CassioSStella/Robo-Sumo_Eletronica/Exemplo/Sumo_Geral_Modular.kicad_sch

## KiCad design Exemplo/Sumo_Geral_Modular.kicad_sch (2026-05-20)

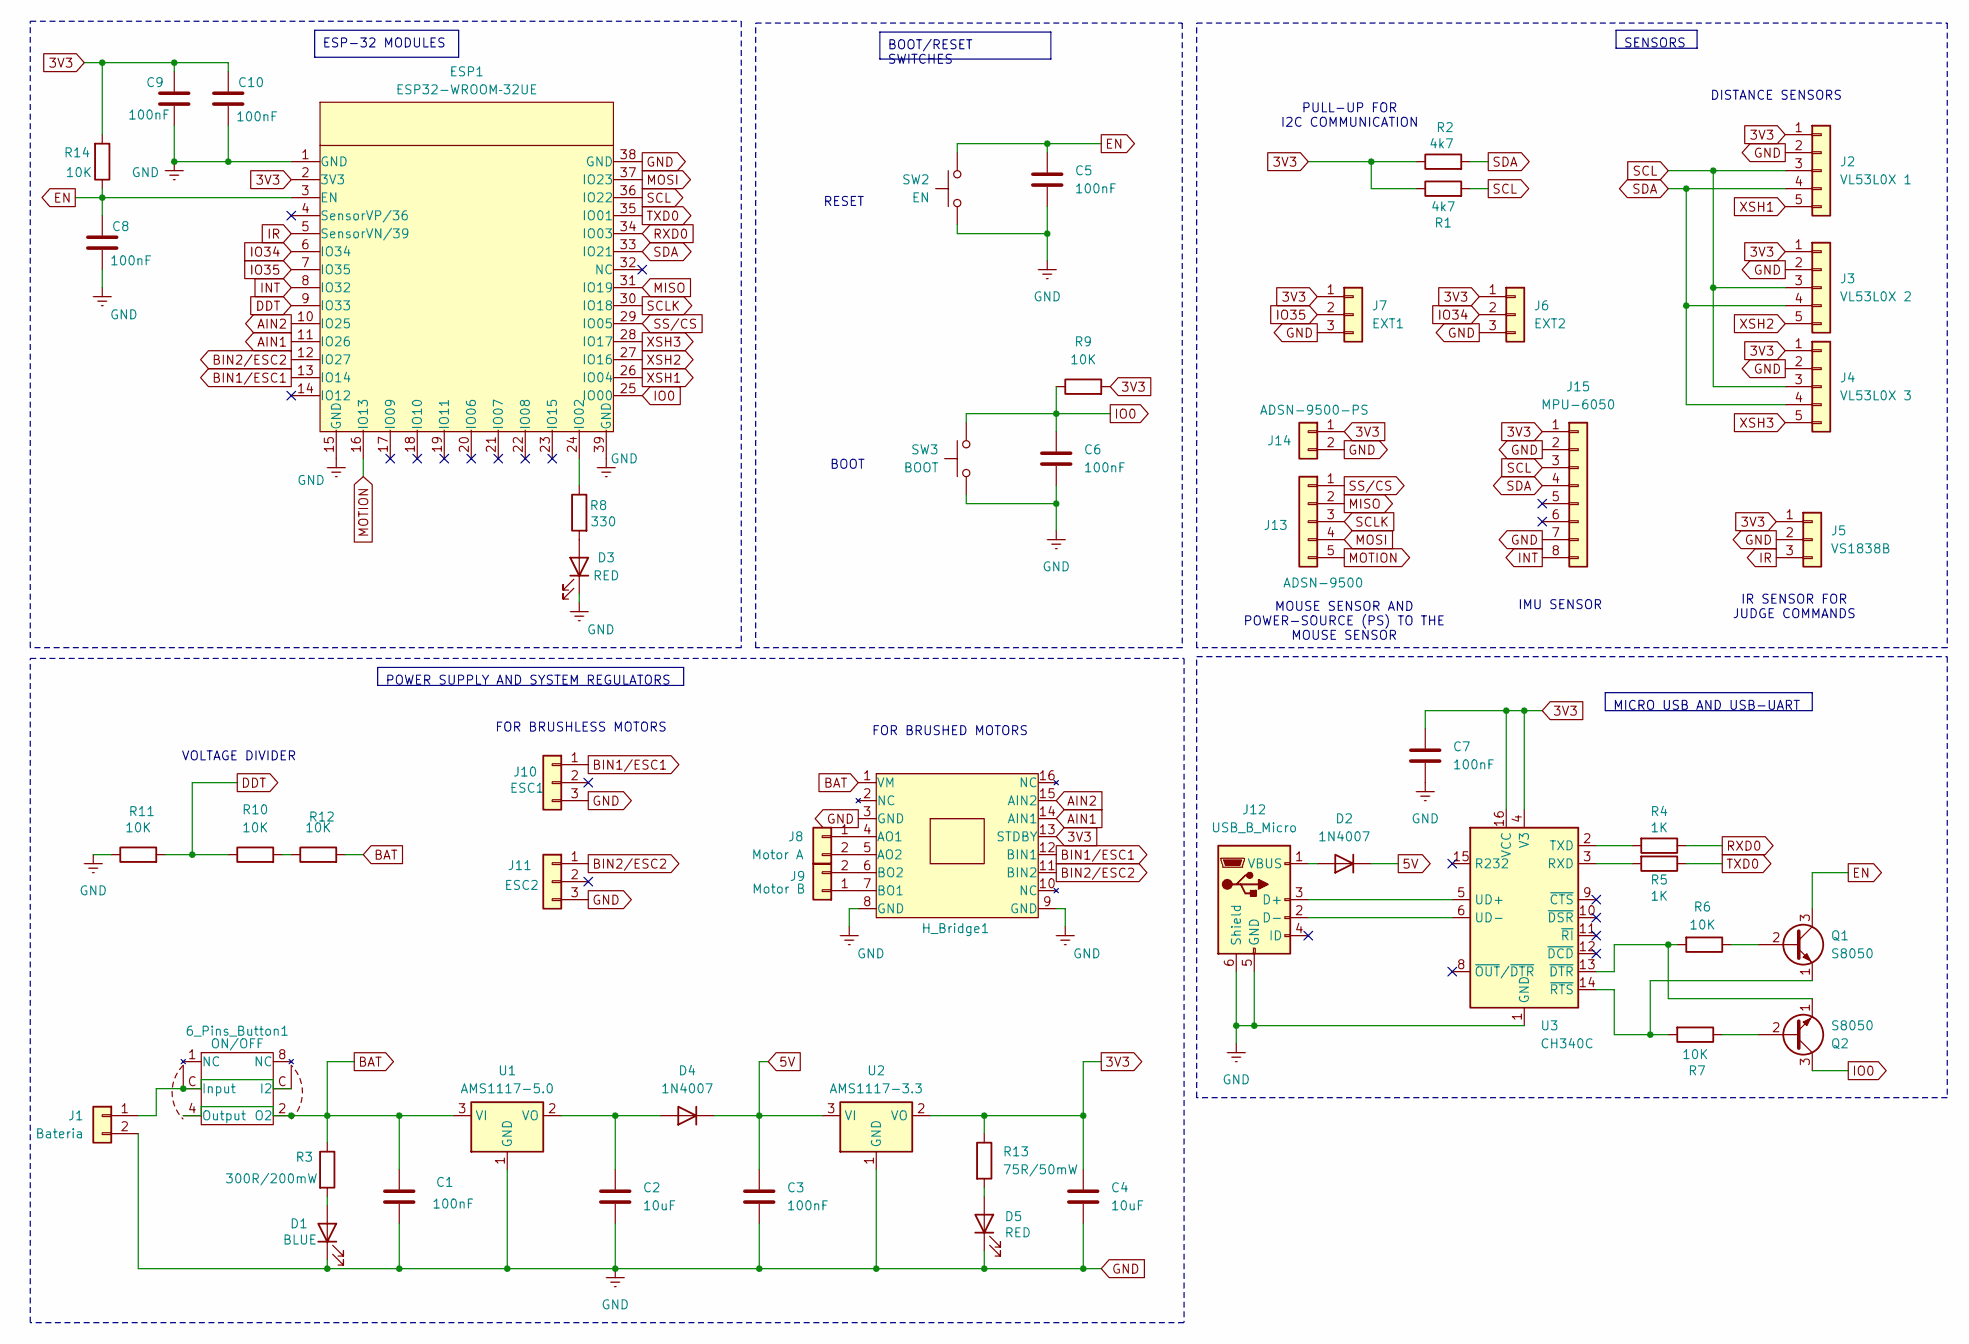
[picture p9: schematic Sumo_Geral_Modular.kicad_sch]

Parts:
6_Pins_Button1: ON/OFF; Push_Button_6_pins
C1, C3, C5, C6, C7, C8, C9, C10: 100nF; C_0603_1608Metric
C2, C4: 10uF; C_0603_1608Metric
D1: BLUE; LED_0603_1608Metric
D2, D4: 1N4007; D_0603_1608Metric
D3, D5: RED; LED_0603_1608Metric
ESP1: ESP32-WROOM­32UE; ESP32-WROOM-32
H_Bridge1: H_Bridge_with_headers
J1: Bateria; JST_PH_B2B-PH-K_1x02_P2.00mm_Vertical
J2: VL53L0X 1; JST_XH_B5B-XH-A_1x05_P2.50mm_Vertical
J3: VL53L0X 2; JST_XH_B5B-XH-A_1x05_P2.50mm_Vertical
J4: VL53L0X 3; JST_XH_B5B-XH-A_1x05_P2.50mm_Vertical
J5: VS1838B; PinHeader_1x03_P2.00mm_Vertical
J6: EXT2; PinHeader_1x03_P2.00mm_Vertical
J7: EXT1; PinHeader_1x03_P2.00mm_Vertical
J8: Motor A; JST_XH_B2B-XH-A_1x02_P2.50mm_Vertical
J9: Motor B; JST_XH_B2B-XH-A_1x02_P2.50mm_Vertical
J10: ESC1; JST_XH_B3B-XH-A_1x03_P2.50mm_Vertical
J11: ESC2; JST_XH_B3B-XH-A_1x03_P2.50mm_Vertical
J12: USB_B_Micro; USB_Micro-B_Amphenol_10118194_Horizontal
J13: ADSN-9500; JST_XH_S5B-XH-A_1x05_P2.50mm_Horizontal
J14: ADSN-9500-PS; JST_XH_S2B-XH-A_1x02_P2.50mm_Horizontal
J15: MPU-6050; PinSocket_1x08_P2.54mm_Vertical
Q1, Q2: S8050; SOT-23
R1, R2: 4k7; R_0603_1608Metric
R3: 300R/200mW; R_0603_1608Metric
R4, R5: 1K; R_0603_1608Metric
R6, R7, R9, R11, R12, R14: 10K; R_0603_1608Metric
R8: 330; R_0603_1608Metric
R10: 10K; C_0603_1608Metric
R13: 75R/50mW; R_0603_1608Metric
SW2: EN; SW_SPST_TL3305C
SW3: BOOT; SW_SPST_TL3305C
U1: AMS1117-5.0; SOT-223-3_TabPin2
U2: AMS1117-3.3; SOT-223-3_TabPin2
U3: CH340C; SOIC-16_3.9x9.9mm_P1.27mm

Connections:
3V3: C4.1, C7.1, C9.1, C10.1, ESP1.2 (3V3), H_Bridge1.13 (STDBY), J2.1, J3.1, J4.1, J5.1, J6.1, J7.1, J14.1, J15.1, R1.1, R2.1, R9.2, R13.1, R14.2, U2.2 (VO), U3.4 (V3), U3.16 (VCC)
5V: C3.1, D2.1 (K), D4.1 (K), U2.3 (VI)
AIN1: ESP1.11 (IO26), H_Bridge1.14 (AIN1)
AIN2: ESP1.10 (IO25), H_Bridge1.15 (AIN2)
BAT: 6_Pins_Button1.2 (O2), 6_Pins_Button1.4 (Output), C1.1, H_Bridge1.1 (VM), R3.1, R12.2, U1.3 (VI)
BIN1/ESC1: ESP1.13 (IO14), H_Bridge1.12 (BIN1), J10.1
BIN2/ESC2: ESP1.12 (IO27), H_Bridge1.11 (BIN2), J11.1
DDT: ESP1.9 (IO33), R10.1, R11.2
EN: C5.2, C8.1, ESP1.3 (EN), Q1.3 (C), R14.1, SW2.1
GND: C1.2, C2.2, C3.2, C4.2, C5.1, C6.2, C7.2, C8.2, C9.2, C10.2, D1.1 (K), D3.1 (K), D5.1 (K), ESP1.1 (GND), ESP1.15 (GND), ESP1.38 (GND), ESP1.39 (GND), H_Bridge1.3 (GND), H_Bridge1.8 (GND), H_Bridge1.9 (GND), J1.2, J2.2, J3.2, J4.2, J5.2, J6.3, J7.3, J10.3, J11.3, J12.5 (GND), J12.6 (Shield), J14.2, J15.2, J15.7, R11.1, SW2.2, SW3.2, U1.1 (GND), U2.1 (GND), U3.1 (GND)
INT: ESP1.8 (IO32), J15.8
IO0: C6.1, ESP1.25 (IO00), Q2.3 (C), R9.1, SW3.1
IO34: ESP1.6 (IO34), J6.2
IO35: ESP1.7 (IO35), J7.2
IR: ESP1.5 (SensorVN/39), J5.3
MISO: ESP1.31 (IO19), J13.2
MOSI: ESP1.37 (IO23), J13.4
MOTION: ESP1.16 (IO13), J13.5
unnamed: 6_Pins_Button1.C (I2), J1.1
unnamed: C2.1, D4.2 (A), U1.2 (VO)
unnamed: D1.2 (A), R3.2
unnamed: D2.2 (A), J12.1 (VBUS)
unnamed: D3.2 (A), R8.2
unnamed: D5.2 (A), R13.2
unnamed: ESP1.24 (IO02), R8.1
unnamed: H_Bridge1.4 (AO1), J8.1
unnamed: H_Bridge1.5 (AO2), J8.2
unnamed: H_Bridge1.6 (BO2), J9.2
unnamed: H_Bridge1.7 (BO1), J9.1
unnamed: J12.2 (D-), U3.6 (UD-)
unnamed: J12.3 (D+), U3.5 (UD+)
unnamed: Q1.1 (E), R7.2, U3.14 (~RTS)
unnamed: Q1.2 (B), R6.1
unnamed: Q2.1 (E), R6.2, U3.13 (~DTR)
unnamed: Q2.2 (B), R7.1
unnamed: R4.2, U3.2 (TXD)
unnamed: R5.2, U3.3 (RXD)
unnamed: R10.2, R12.1
RXD0: ESP1.34 (IO03), R4.1
SCL: ESP1.36 (IO22), J2.3, J3.3, J4.3, J15.3, R1.2
SCLK: ESP1.30 (IO18), J13.3
SDA: ESP1.33 (IO21), J2.4, J3.4, J4.4, J15.4, R2.2
SS/CS: ESP1.29 (IO05), J13.1
TXD0: ESP1.35 (IO01), R5.1
XSH1: ESP1.26 (IO04), J2.5
XSH2: ESP1.27 (IO16), J3.5
XSH3: ESP1.28 (IO17), J4.5

Notes on the sheet:
SENSORS
ESP-32 MODULES
BOOT/RESET SWITCHES
MICRO USB AND USB-UART
POWER SUPPLY AND SYSTEM REGULATORS
MOUSE SENSOR AND POWER-SOURCE (PS) TO THE MOUSE SENSOR
FOR BRUSHLESS MOTORS
VOLTAGE DIVIDER
FOR BRUSHED MOTORS
PULL-UP FOR I2C COMMUNICATION
IR SENSOR FOR JUDGE COMMANDS
IMU SENSOR
DISTANCE SENSORS
BOOT
RESET
